UniversalScientificTechnologies/AIRDOSC01/hw/cad/SIPMBOX01B/assembly.scad

use <src/SIPMBOX01B.scad>


include <configuration.scad>


SIPMBOX01B();
