UniversalScientificTechnologies/AIRDOSC01/hw/cad/SIPMBOX01C/assembly.scad

use <src/SIPMBOX01C.scad>


include <configuration.scad>


SIPMBOX01C_D08();

SIPMBOX01C_D07();
