UniversalScientificTechnologies/AIRDOSC01/hw/cad/SIPMBOX02B/assembly.scad

use <src/SIPMBOX01A.scad>


include <configuration.scad>


SIPMBOX01A();
