UniversalScientificTechnologies/AIRDOSC01/hw/cad/SIPMBOX01A/print_data/SIPMBOX01A.scad

use <../src/SIPMBOX01A.scad>

include <../configuration.scad>

SIPMBOX01A();
