UniversalScientificTechnologies/AIRDOSC01/hw/cad/SIPMBOX02B/print_data/SIPMBOX01C_D05.scad

use <../src/SIPMBOX01C.scad>

include <../configuration.scad>

SIPMBOX01C_D05();
